musashimm/aquamat/files/aquamat_control_connector.png

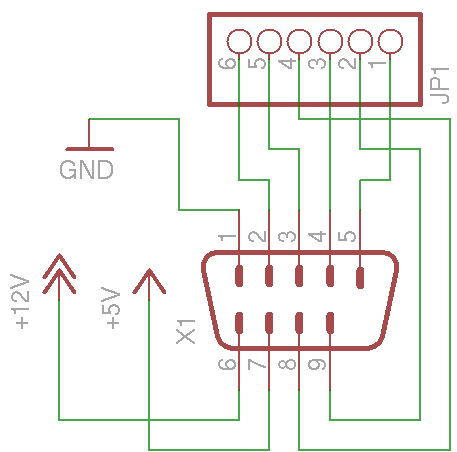
files/aquamat_control_connector.png
