musashimm/aquamat/files/atmega32.png

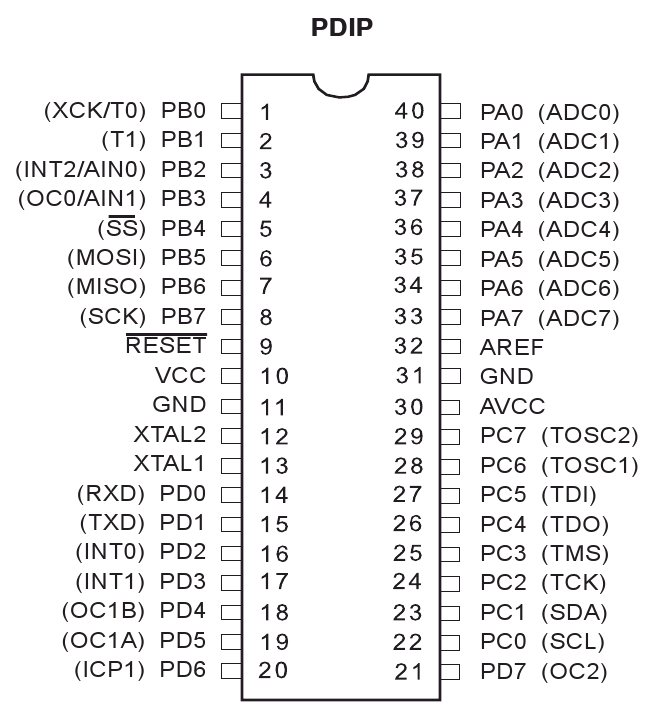
files/atmega32.png
