musashimm/aquamat/files/control_connector.jpg

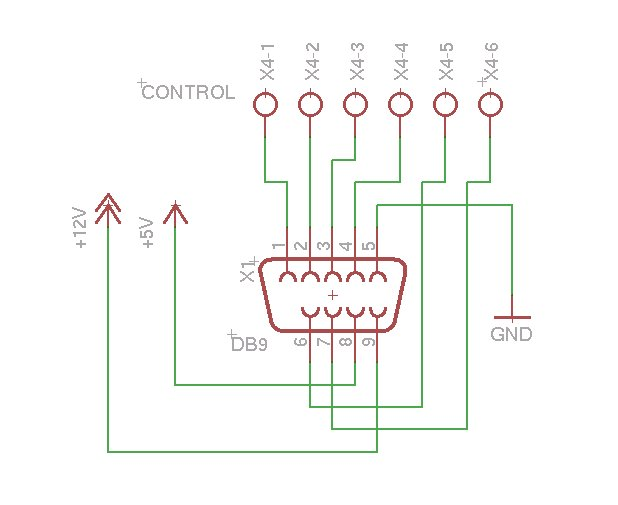
files/control_connector.jpg
