musashimm/aquamat/files/functions.png

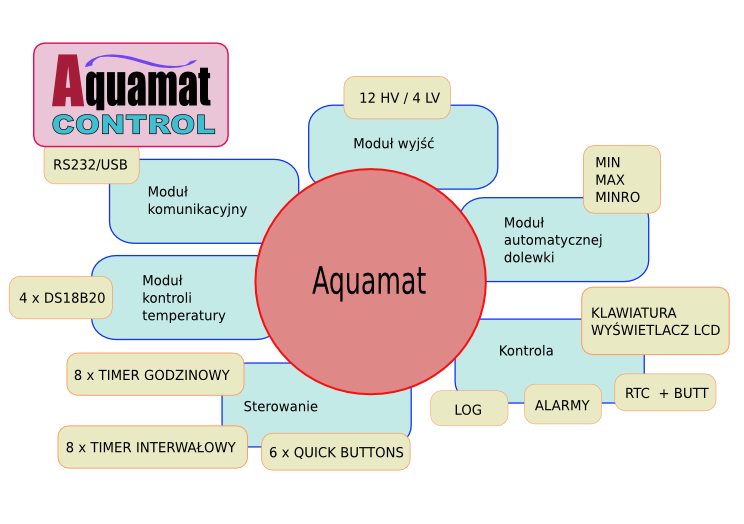
files/functions.png
