musashimm/aquamat/files/jack_ad.jpg

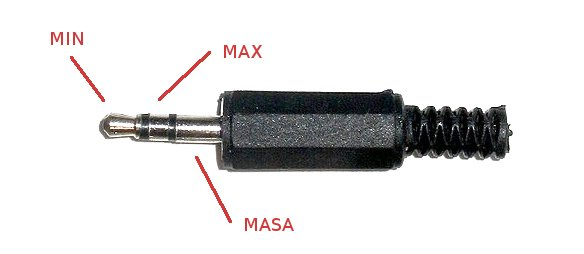
files/jack_ad.jpg
