musashimm/aquamat/files/top_off.png

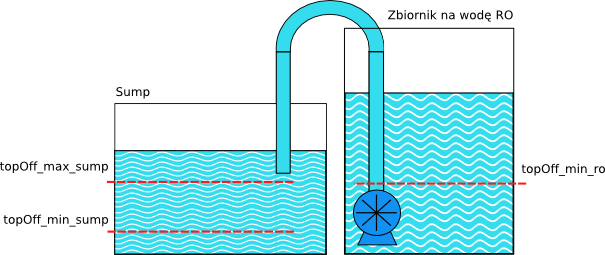
files/top_off.png
