musashimm/aquamat/software/pwm.c

/*
    Aquamat - Sterownik akwariowy Open Source
    Copyright (C) 2009 Wojciech Todryk (wojciech@todryk.pl)

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
	$Id$
*/

#include <avr/interrupt.h>
#include "pwm.h"
#include "menu.h"
#include "eeprom.h"
#include "timerssec.h"
#include "strings.h"
#include "hd44780.h"
#include "commandsDefs.h"
#include "eeprom.h"
#include "comm_gui.h"

/** @file pwm.c
	@brief Implementacja wyjść PWM.

	Ze względu na "programową obsługę PWM" struktura PWM jest bezpośrednio skojarzona z portem mikrokontrolera. Definicja \ref PWM_PORT określa, który port będzie portem PWM. Definicja \ref PWM_PINS określa, które porty będą PWM. Index struktury \ref PWM określa jednocześnie jaki pin obsługuje. Przykładowo index 0 przypisany jest do pinu 0 w porcie \ref PWM_PORT. Blokada wyjścia PWM, blokuje zmiany szerokości impulsu wyjścia PWM przez scenariusze. Umożliwia to zmianę np. chwilową wartości PWM, nawet jak wcześniej był przypisany jakiś scenariusz do tego wyjścia.
*/

extern uint8_t clock10ms;

/** @var struct PWM pwms
	@brief Tablica przechowująca struktury PWM.

	Index wyjścia PWM odpowiada pinowi w porcie \ref PWM_PORT.
*/
struct PWM pwms[PWM_NUM];

/** Inicjalizacja wyjść PWM
*/
void pwm_init(void) {

	PWM_DDR |= PWM_PINS;

	TCCR0 = _BV(WGM01) |_BV(CS01);	// clock / 8 - wyserowanie na porównanie 1/8000000*25*8*4*100
	OCR0 = PWM_TIMER_TAU;			// wartość licznika CTC
	TIMSK |= _BV(OCIE0);			// przerwanie na porównanie
}

/** Procedura przerwania ustawiająca pwm na porcie.
*/
ISR (TIMER0_COMP_vect) {

	static volatile uint8_t clock1_4_1_10ms;
	static volatile uint8_t clock1_10ms;
	uint8_t i;

	if(!(--clock1_4_1_10ms)) {
		clock1_4_1_10ms = 4;
		if(!(--clock1_10ms)) {
			clock1_10ms = 100;
		}
		for (i=0;i < PWM_NUM;i++) {
			if (clock1_10ms <= pwms[i].width) {
				PWM_PORTOUT |= _BV(i);
			} else {
				PWM_PORTOUT &= ~_BV(i);
			}
		}
	}
}

/** Ustawia żądaną wartość PWM na wyjście.
	@param uint8_t oidx index wyjścia,
	@param uint8_t pwm wartość PWM.
*/
void pwm_set(uint8_t oidx,uint8_t pwm) {
	if (oidx < PWM_NUM) {
		pwms[oidx].width = pwm;
	}
}

/** Wyświetlanie i konfiguracja wyjść PWM
*/
void ui_pwm_settings_display(void) {

	if (!MENU_F(MENU_VARS_LOADED_FLAG)) {
		load_name(menu_unit() * EEPROM_PWM_SIZE + EEPROM_PWM_SETTINGS_BEGIN + EEPROM_PWM_NAME_OFFSET);
		MENU_SF(MENU_VARS_LOADED_FLAG);
	}

	hd44780_label(OUTPWM_S,FALSE,FALSE);
	hd44780_out4hex(menu_unit()+1);
	hd44780_outstrn_P(SPACE_S);
	hd44780_outstrn_P(PSTR("P="));
	hd44780_out8dec3(pwms[menu_unit()].width);
	hd44780_outstrn_P(PSTR("%"));
	hd44780_next_line();
	hd44780_outstrn_P(SPACE_S);
	hd44780_label(BL_S,FALSE,FALSE);
	hd44780_switch_state(pwm_check_flag(menu_unit(),PWM_FLAG_BLOCKED),FALSE);
	hd44780_outstrn_P(SPACE_S);
	hd44780_label(NZW_S,TRUE,FALSE);
	hd44780_outstrn(name);
	hd44780_outstrn_P(PAR_S);

	switch (menu_phase()) {
	case 0:
		menu_standard_unit(PWM_NUM);
		break;
	case 1:
		menu_set_phase();
		break;
	case 2:
		menu_mod_uint8(1,13,&pwms[menu_unit()].width,0,PWM_MAX_WIDTH,FALSE);
		break;
	case 3:
		menu_mod_bit(2,5,&(pwms[menu_unit()].flags),PWM_FLAG_BLOCKED);
		break;
	case 4:
	case 5:
	case 6:
	case 7:
	case 8:
		menu_mod_char(2,12,name,4);
		break;
	case 9:
		save_pwm_settings(menu_unit() * EEPROM_PWM_SIZE + EEPROM_PWM_SETTINGS_BEGIN,menu_unit());
		save_name(menu_unit() * EEPROM_PWM_SIZE + EEPROM_PWM_SETTINGS_BEGIN + EEPROM_PWM_NAME_OFFSET);
		menu_reset_phase();
	}
}

/** Wczytuje konfigurację wszystkich wyjść PWM.
*/
void load_pwms_settings(uint16_t addr) {
	uint8_t i;
 	for (i=0;i < PWM_NUM;i++) {
 		load_pwm_settings(i * EEPROM_PWM_SIZE + addr,i);
 	}
}

/** Zapisuje konfigurację wszystkich wyjść PWM.
*/
void save_pwms_settings (uint16_t addr) {
	uint8_t i;
 	for (i=0;i < PWM_NUM;i++) {
 		save_pwm_settings(i * EEPROM_PWM_SIZE + addr,i);
 	}
}

/** Zapisuje konfigurację jednego wyjścia PWM.
	@param uint16_t base_addr adres bazowy, pod który będzie zapisana konfiguracja
	@param uint8_t o index wyjścia PWM.
*/
void save_pwm_settings(uint16_t base_addr,uint8_t o) {
	eeprom_write_byte(base_addr + EEPROM_PWM_WIDTH_OFFSET,pwms[o].width);
	eeprom_write_byte(base_addr + EEPROM_PWM_FLAGS_OFFSET,pwms[o].flags & PWM_FLAG_CONFIG_MASK);
}

/** Wczytuje konfigurację wszystkich wyjść PWM.
	@param uint16_t addr adres, pod którym zostanie zapisana konfiguracja
	@param uint8_t o index wyjścia PWM.
*/
void load_pwm_settings(uint16_t base_addr, uint8_t o) {
	pwms[o].width = eeprom_read_byte(base_addr + EEPROM_PWM_WIDTH_OFFSET);
	if (pwms[o].width > PWM_MAX_WIDTH) {
		pwms[o].width = 0;
	}
	pwms[o].flags = eeprom_read_byte(base_addr + EEPROM_PWM_FLAGS_OFFSET) & PWM_FLAG_CONFIG_MASK;
}

/** Sprawdza poszczególne flagi
	@param id numer wyjścia pwm
	@param flag flaga
*/
uint8_t pwm_check_flag(uint8_t id,uint8_t flag) {
    if (id >= PWM_NUM) {
        return 1;
    } else {
        return pwms[id].flags & _BV(flag);
    }
}

/** Status wyjść PWM.
*/
void pwm_status_display(void) {
	pwm_status(0);
	pwm_status(1);
	hd44780_goto(2,1);
	pwm_status(2);
	pwm_status(3);
}

/** Status pojedynczego wyjścia.
	@param uint8_t o index wyjscia PWM.
*/
void pwm_status(uint8_t o) {
	hd44780_outstrn_P(SPACE_S);
	hd44780_switch_state(pwm_check_flag(o,PWM_FLAG_BLOCKED),FALSE);
	hd44780_outstrn_P(SPACE_S);
	hd44780_out8dec3(pwms[o].width);
	hd44780_outstrn_P(PSTR("%"));
	hd44780_outstrn_P(SPACE_S);
}

void pwm_gui_get_status(void) {
	uint8_t i;
	gui_command_start(GUI_PWM_COMMAND,GUI_SUBCOMMAND_GET_STATUS_RESPONSE);
	for (i=0;i<PWM_NUM;i++) {
		gui_command_data(pwms[i].width);
		gui_command_data(pwms[i].flags);
	}
	gui_command_end();
	gui_cm_return_status(GUI_COMMAND_OK,GUI_PWM_COMMAND,GUI_SUBCOMMAND_GET_STATUS);
}

void pwm_gui_get_settings(void) {
	uint8_t i,j;
	gui_command_start(GUI_PWM_COMMAND,GUI_SUBCOMMAND_GET_SETTINGS_RESPONSE);
	for (i=0;i<PWM_NUM;i++) {
		gui_command_data(pwms[i].width);
		gui_command_data(pwms[i].flags);
		load_name(i * EEPROM_PWM_SIZE + EEPROM_PWM_NAME_OFFSET + EEPROM_PWM_SETTINGS_BEGIN);
		for(j=0;j<NAME_LENGTH;j++) {
			gui_command_data(name[j]);
		}
	}
	gui_command_end();
	gui_cm_return_status(GUI_COMMAND_OK,GUI_PWM_COMMAND,GUI_SUBCOMMAND_GET_SETTINGS);
}

void pwm_gui_set(void) {
	uint8_t i,id;
	id = gui_get_first();
	pwms[id].width = gui_get_next();
	pwms[id].flags = gui_get_next();
	save_pwm_settings(id * EEPROM_PWM_SIZE + EEPROM_PWM_SETTINGS_BEGIN,id);

	for(i=0;i<NAME_LENGTH;i++) {
		name[i] = gui_get_next();
	}
	save_name(id * EEPROM_PWM_SIZE + EEPROM_PWM_NAME_OFFSET + EEPROM_PWM_SETTINGS_BEGIN);
	gui_cm_return_status_unit(GUI_COMMAND_OK,GUI_PWM_COMMAND,GUI_SUBCOMMAND_SET,id);
}

void pwm_gui_set_state(void) {
	uint8_t id;
	id = gui_get_first();
	pwms[id].width = gui_get_next();
	pwms[id].flags = gui_get_next();
	gui_cm_return_status_unit(GUI_COMMAND_OK,GUI_PWM_COMMAND,GUI_SUBCOMMAND_SET_STATE,id);
}
