musashimm/aquamat/software/strings.h

/*
    Aquamat - Sterownik akwariowy Open Source
    Copyright (C) 2009 Wojciech Todryk (wojciech@todryk.pl)

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
	$Id: com_menu.c 41 2009-02-23 23:01:59Z musashi@todryk.pl $
*/

/** @file strings.h
	@brief Plik nagłówkowy - Definicje stringów używanych w programie.
*/

extern PGM_P RTC_WDAYS_STRS[];

extern PROGMEM char AKT_S[];
extern PROGMEM char BL_S[];
extern PROGMEM char NZW_S[];
extern PROGMEM char QB_S[];
extern PROGMEM char ALARM_S[];
extern PROGMEM char CENTURY_S[];
extern PROGMEM char COLON_S[];
extern PROGMEM char COOLING_S[];
extern PROGMEM char DAYTIME_S[];
extern PROGMEM char DOT_S[];
extern PROGMEM char EVERYDAY_S[];
extern PROGMEM char EXCLEMATION_S[];
extern PROGMEM char FAILURE_S[];
extern PROGMEM char FROM_S[];
extern PROGMEM char GROUP_S[];
extern PROGMEM char HEATING_S[];
extern PROGMEM char INTEMPSENS_S[];
extern PROGMEM char INT_MIN_S[];
extern PROGMEM char INT_OFF_S[];
extern PROGMEM char INT_ON_S[];
extern PROGMEM char MAX_S[];
extern PROGMEM char MIN_S[];
extern PROGMEM char MINUS_S[];
extern PROGMEM char MINUSMINUS_S[];
extern PROGMEM char MINUSMINUSMINUS_S[];
extern PROGMEM char NNN_S[];
extern PROGMEM char NN_S[];
extern PROGMEM char NONE_S[];
extern PROGMEM char NOTIFY_S[];
extern PROGMEM char NPAR_S[];
extern PROGMEM char N_S[];
extern PROGMEM char OFF_S[];
extern PROGMEM char OK_S[];
extern PROGMEM char OUT_NONAME_S[];
extern PROGMEM char ON_S[];
extern PROGMEM char OUT_S[];
extern PROGMEM char OUTPWM_S[];
extern PROGMEM char PAR_S[];
extern PROGMEM char RO_S[];
extern PROGMEM char SLASH_S[];
extern PROGMEM char SPACE_S[];
extern PROGMEM char START_S[];
extern PROGMEM char STATUS_ACTIVE_S[];
extern PROGMEM char STATUS_BAD_OUT_S[];
extern PROGMEM char STATUS_BAD_TIME_S[];
extern PROGMEM char STATUS_BAD_WDAY[];
extern PROGMEM char STATUS_BLOCKED_S[];
extern PROGMEM char STATUS_NOTACTIVE_S[];
extern PROGMEM char STATUS_OUT_BLOCKED_S[];
extern PROGMEM char STATUS_S[];
extern PROGMEM char STATUS_STATUS_ALREADY_BUSY_S[];
extern PROGMEM char TEMP_CURRENT_S[];
extern PROGMEM char TEMP_FLAGS_S[];
extern PROGMEM char TEMP_HISTERESIS_S[];
extern PROGMEM char TEMP_MAX_S[];
extern PROGMEM char TEMP_MIN_S[];
extern PROGMEM char TEMP_SENSOR_S[];
extern PROGMEM char TEMP_TARGET_NIGHT_S[];
extern PROGMEM char TEMP_TARGET_S[];
extern PROGMEM char TEMP_TEMP_S[];
extern PROGMEM char TIMER_S[];
extern PROGMEM char TO_S[];
extern PROGMEM char TOP_OFF_MAX_RUN_S[];
extern PROGMEM char UINT8_BAD_S[];
extern PROGMEM char UNKNOWN_S[];
extern PROGMEM char WDAY_S[];
